BhoumikAcharya/Smart_Signage_Boards/PCB/PCB_V3/3D Models/ams1117-3-3v-2.snapshot.1/AMS1117_render.png

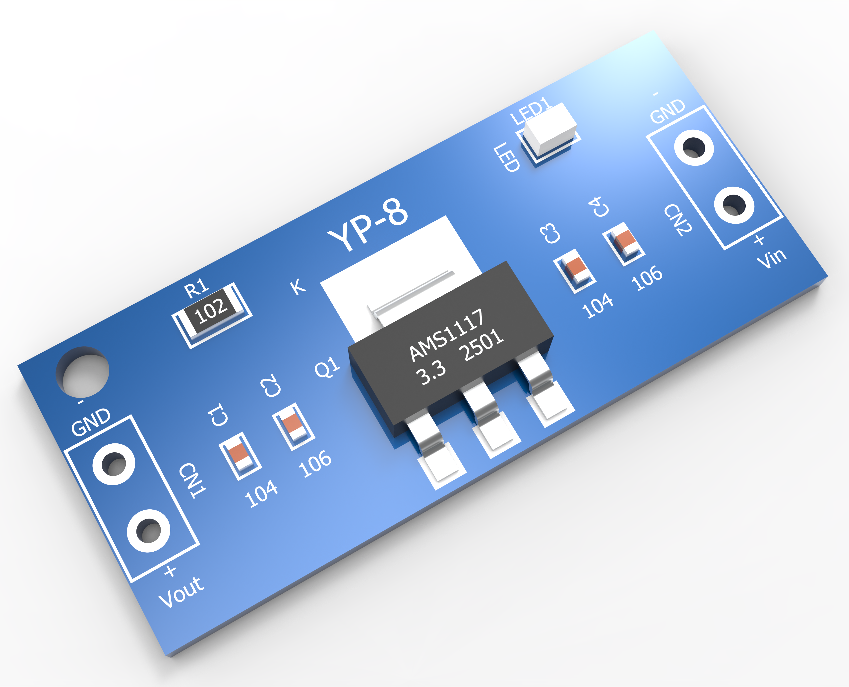
PCB/PCB_V3/3D Models/ams1117-3-3v-2.snapshot.1/AMS1117_render.png
