BhoumikAcharya/Smart_Signage_Boards/PCB/PCB_V3/3D Models/esp32-wroom-cp2102-30pins-1.snapshot.3/esp32_Wroom_CP2102_USMmicro.png

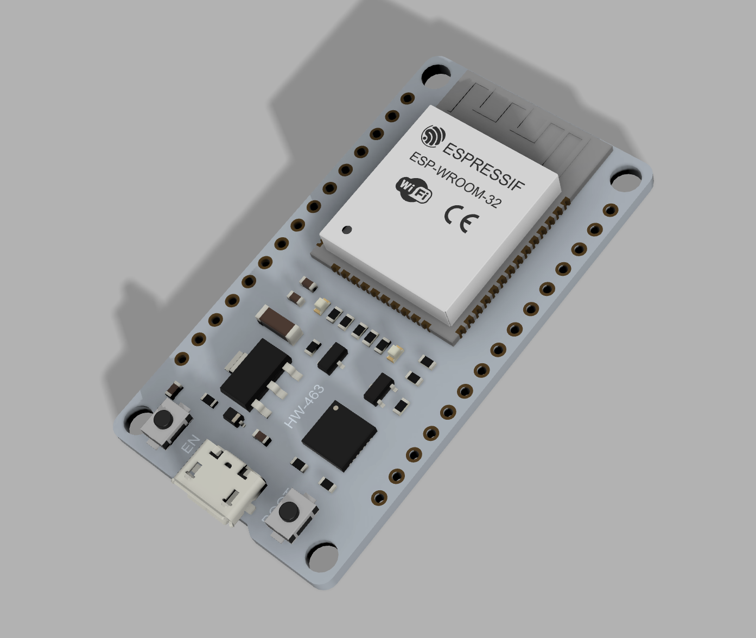
PCB/PCB_V3/3D Models/esp32-wroom-cp2102-30pins-1.snapshot.3/esp32_Wroom_CP2102_USMmicro.png
