BhoumikAcharya/Smart_Signage_Boards/PCB/PCB_V3/3D Models/lan8720-ethernet-board-1.snapshot.3/lan8720_view2.png

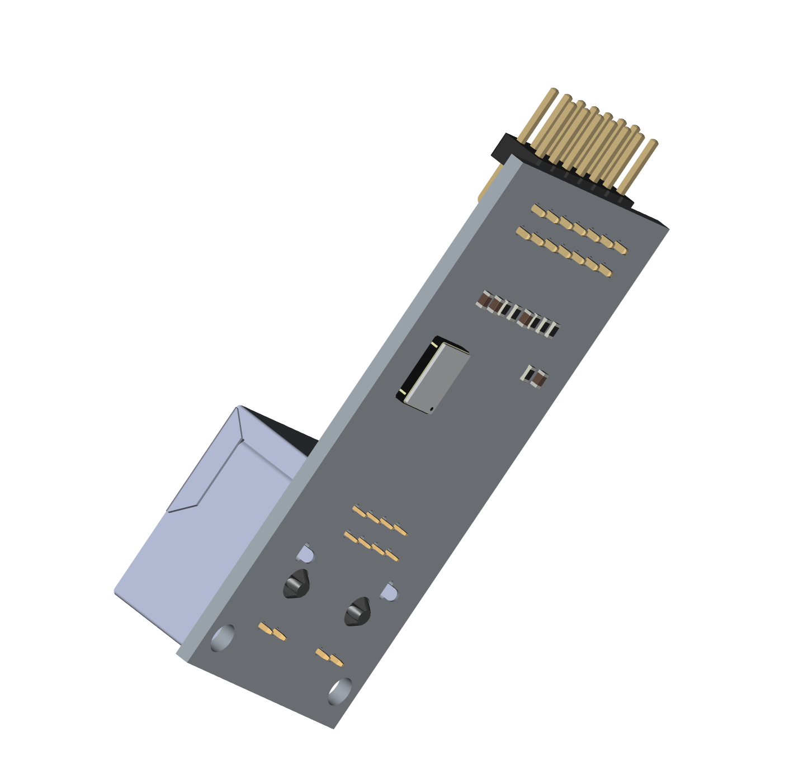
PCB/PCB_V3/3D Models/lan8720-ethernet-board-1.snapshot.3/lan8720_view2.png
