BhoumikAcharya/Smart_Signage_Boards/PCB/PCB_V3/3D Models/d-sun-dc-dc-step-down-voltage-regulator-simple-version-1.snapshot.4/components/Induct_7.2x7.2x3.0mm_simple.step

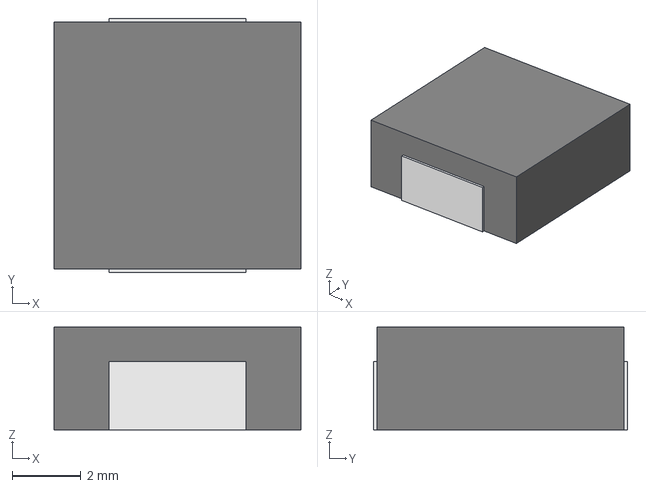
[picture p37: CAD file, 2026-07-13]
PCB/PCB_V3/3D Models/d-sun-dc-dc-step-down-voltage-regulator-simple-version-1.snapshot.4/components/Induct_7.2x7.2x3.0mm_simple.step
7.20 x 7.40 x 3.00 mm
