BhoumikAcharya/Smart_Signage_Boards/PCB/PCB_V3/3D Models/d-sun-dc-dc-step-down-voltage-regulator-simple-version-1.snapshot.4/components/R0603_simple.step

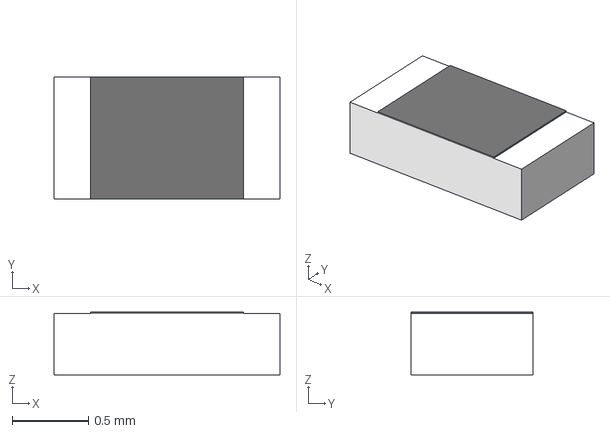
[picture p39: CAD file, 2026-07-13]
PCB/PCB_V3/3D Models/d-sun-dc-dc-step-down-voltage-regulator-simple-version-1.snapshot.4/components/R0603_simple.step
1.48 x 0.8 x 0.41 mm
